minakhan01/PAL_Wearable_Opensource/Raspberry_Pi/Electronics/Raspi_shield/PAL_shield.sch

## KiCad design Raspberry_Pi/Electronics/Raspi_shield/PAL_shield.sch (2020-07-10)

Schematic: PAL_shield.sch

Parts:
J1: Conn_02x20_Odd_Even; PinHeader_2x20_P2.54mm_Vertical
J2: Conn_01x06; PinHeader_1x06_P2.54mm_Vertical
J3: Conn_01x08; PinHeader_1x08_P2.54mm_Vertical
J4: Conn_02x08_Odd_Even; PinHeader_2x08_P2.54mm_Vertical
J5: Conn_02x03_Odd_Even; PinHeader_2x03_P2.54mm_Vertical
J6: Conn_01x03; PinHeader_1x03_P2.54mm_Vertical
U1: MCP3008; SOIC-16_3.9x9.9mm_P1.27mm

Notes on the sheet:
3V3 SDA SCL GND LED 3V3 MOSI MISO SCLK GND PWM MISO1 GND
5V 5V BUTTON BCLK GND SPI (CS0) GND MOSI1
