minakhan01/PAL_Wearable_Opensource/Raspberry_Pi/Electronics/mic_board/PAL_mic_board_v1.sch

## KiCad design Raspberry_Pi/Electronics/mic_board/PAL_mic_board_v1.sch (2020-07-10)

Schematic: PAL_mic_board_v1.sch

Parts:
D1: LED; LED_0603_1608Metric
J1: Conn_01x09; PinHeader_1x09_P2.54mm_Vertical
R1: R; R_0603_1608Metric
SW1: SW_Push; SW_PUSH_6mm
